CoretechR/Keybon/keybon/bmp.h

unsigned char bmp_swap[384];


static const unsigned char PROGMEM bmp_backward[] =
{
  0x00, 0x00, 0x00, 0x00, 0x00, 0x00, 0x00, 0x00, 0x00, 0x00, 0x00, 0x00, 0x00, 0x00, 0x00, 0x00, 
  0x00, 0x00, 0x00, 0x00, 0x00, 0x00, 0x00, 0x00, 0x00, 0x00, 0x00, 0x00, 0x00, 0x00, 0x00, 0x00, 
  0x00, 0x00, 0x00, 0x00, 0x00, 0x00, 0x00, 0x00, 0x00, 0x00, 0x00, 0x00, 0x00, 0x00, 0x00, 0x00, 
  0x00, 0x00, 0x00, 0x00, 0x00, 0x00, 0x00, 0x00, 0x00, 0x00, 0x00, 0x00, 0x00, 0x00, 0x00, 0x00, 
  0x00, 0x00, 0x00, 0x00, 0x00, 0x00, 0x00, 0x00, 0x00, 0x00, 0x00, 0x00, 0x00, 0x00, 0x00, 0x00, 
  0x00, 0x00, 0x00, 0x06, 0x00, 0x00, 0x00, 0x60, 0x00, 0x00, 0x00, 0x1e, 0x00, 0x00, 0x01, 0xe0, 
  0x00, 0x00, 0x00, 0x7e, 0x00, 0x00, 0x07, 0xe0, 0x00, 0x00, 0x01, 0xfe, 0x00, 0x00, 0x1f, 0xe0, 
  0x00, 0x00, 0x07, 0xfe, 0x00, 0x00, 0x7f, 0xe0, 0x00, 0x00, 0x1f, 0xfe, 0x00, 0x01, 0xff, 0xe0, 
  0x00, 0x00, 0x7f, 0xfe, 0x00, 0x07, 0xff, 0xe0, 0x00, 0x01, 0xff, 0xfe, 0x00, 0x1f, 0xff, 0xe0, 
  0x00, 0x07, 0xff, 0xfe, 0x00, 0x7f, 0xff, 0xe0, 0x00, 0x1f, 0xff, 0xfe, 0x01, 0xff, 0xff, 0xe0, 
  0x00, 0x7f, 0xff, 0xfe, 0x07, 0xff, 0xff, 0xe0, 0x01, 0xff, 0xff, 0xfe, 0x1f, 0xff, 0xff, 0xe0, 
  0x07, 0xff, 0xff, 0xfe, 0x7f, 0xff, 0xff, 0xe0, 0x0f, 0xff, 0xff, 0xfe, 0xff, 0xff, 0xff, 0xe0, 
  0x07, 0xff, 0xff, 0xfe, 0x7f, 0xff, 0xff, 0xe0, 0x01, 0xff, 0xff, 0xfe, 0x1f, 0xff, 0xff, 0xe0, 
  0x00, 0x7f, 0xff, 0xfe, 0x07, 0xff, 0xff, 0xe0, 0x00, 0x1f, 0xff, 0xfe, 0x01, 0xff, 0xff, 0xe0, 
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
  0x00, 0x00, 0x01, 0xf0, 0x00, 0x00, 0x00, 0x00, 0x00, 0x00, 0x00, 0xf0, 0x00, 0x00, 0x00, 0x00, 
  0x00, 0x00, 0x00, 0x70, 0x00, 0x00, 0x00, 0x00, 0x00, 0x00, 0x00, 0x30, 0x00, 0x00, 0x00, 0x00, 
  0x00, 0x00, 0x00, 0x00, 0x00, 0x00, 0x00, 0x00, 0x00, 0x00, 0x00, 0x00, 0x00, 0x00, 0x00, 0x00
};
